basilfx/DSMR-Splitter/docs/Pictures/Photo2.jpeg

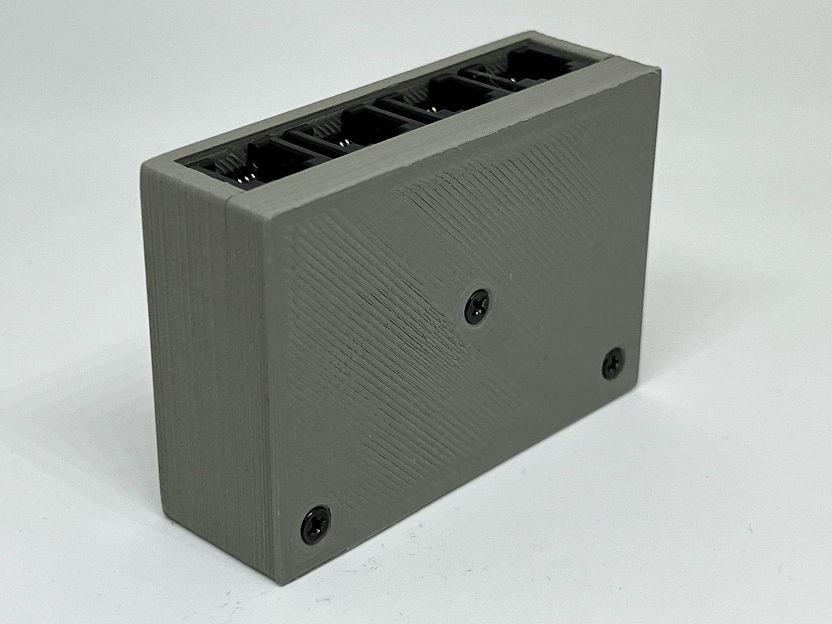
docs/Pictures/Photo2.jpeg
