basilfx/DSMR-Splitter/docs/Pictures/Photo4.jpeg

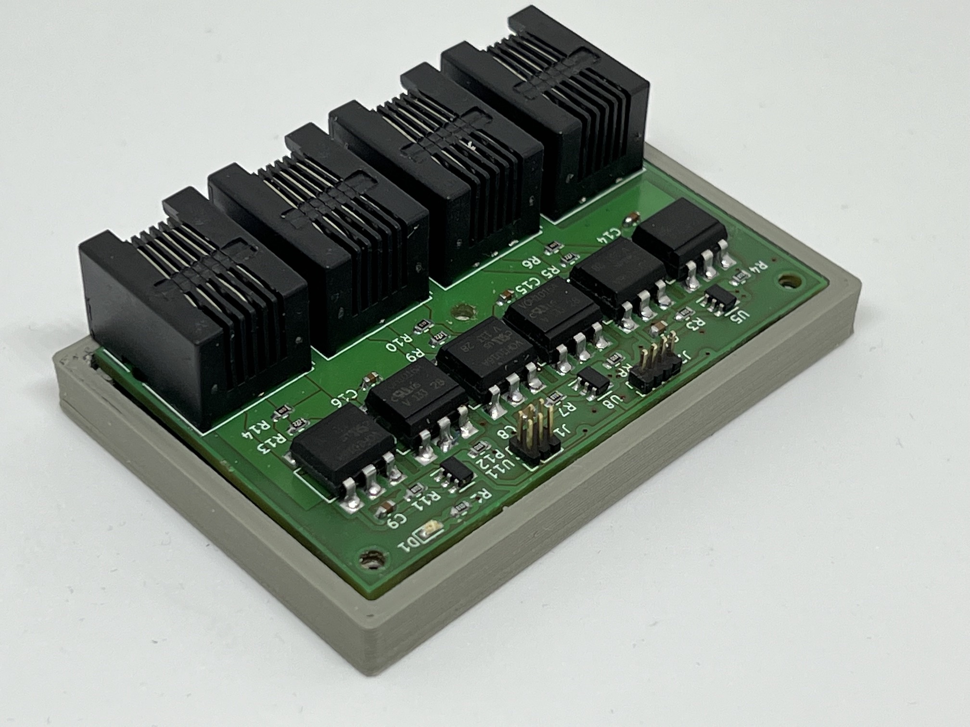
docs/Pictures/Photo4.jpeg
